emsewreinch/gesturaware-kasa/Ekran görüntüsü 2026-09-13 182619.png

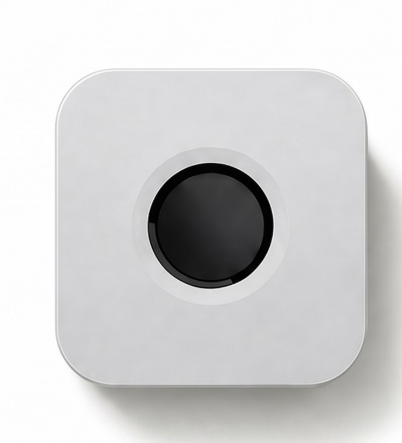
Ekran görüntüsü 2026-09-13 182619.png
