emsewreinch/gesturaware-kasa/kontrolcukasa.scad

// =============================================================
// GesturAware - KONTROLCU KASASI (Controller Edition)
//
// Oyun kontrolcusunun arkasina takilan premium kasa.
// Dis olculer Cihazkasaguncel.scad ile AYNI: 64.74 x 53.5 x 20.6 mm.
// PCB: pcb_v1_headers_z.stl (45 x 40 x 1.6 mm, M2 delikler 39 x 34).
//
// 2 parca, ikisi de destek (support) olmadan basilir:
//
//   KAPAK : ust parca. 45 derece pahli ust kenar, buton cevresinde
//           hale halkasi ve iki yanda "(( o ))" jest dalgalari (oyma).
//           Ic dudak govdeye girer, snap toplariyla kilitlenir ve
//           tirnaklariyla PCB'yi yukaridan bastirir.
//   GOVDE : alt parca. USB-C, LED, sensor/reset delikleri, PCB rafi,
//           PCB v1 montaj deliklerinin altinda ayaklar ve tabandan
//           havsali M2 vida delikleri.
//
// Tum olculer mm. Z=0 kasanin (govdenin) en alti.
// USB-C on (-Y), LED arka (+Y) duvarda.
// =============================================================

$fa = 4;
$fs = 0.35;


// =============================================================
// BILESEN / PCB OLCULERI  (PCB v1, pcb_v1_headers_z.stl'den)
// PCB kasada USB kenari one (-Y) bakacak sekilde, 90 derece
// dondurulmus durur: 40 mm kenar kasada X, 45 mm kenar Y.
// =============================================================

pcb_edge_usb = 40;         // PCB X boyu (USB kenari)
pcb_depth    = 45;         // PCB Y boyu
pcb_thick    = 1.6;
pcb_comp_h   = 6.6;        // PCB ustu en yuksek komponent (buton)

hole_ax = 17;              // PCB montaj delikleri X yari-araligi (34 mm)
hole_ay = 19.5;            // PCB montaj delikleri Y yari-araligi (39 mm)
pcb_hole_d = 2.2;          // PCB delik capi (M2)

usb_edge_off = 8.76;       // USB-C merkezinin PCB merkezinden X kacikligi
usb_cx       = -0.4;       // USB-C acikligi X (PCB bunu takip eder)
usb_z_kart   = 3.25;       // USB-C merkezinin PCB alt yuzunden yuksekligi
pcb_cy       = -0.7;       // PCB merkezi Y (USB-C on duvara ~0.5 mm yakin)

usb_w     = 9.2;           // USB-C acikligi X
usb_bos_h = 3.4;           // USB-C acikligi Z
usb_r     = 1.7;

usb_agiz_w     = 10.5;     // on agiz (kablo govdesi) flare
usb_agiz_h     = 7.0;
usb_agiz_r     = 2.5;
usb_agiz_derin = 2;

floor_gap = 2.0;           // PCB alti bosluk (ayak yuksekligi)

et = 2;                    // duvar kalinligi
tavan_et = 2.6;            // kapak tavani (oyuk altinda 1.4 mm kalir)

buton_cap = 12;            // ust buton deligi
buton_x   = 0;
buton_y   = 0;

sensor_cap = 5.0;          // alt sensor deligi
reset_cap  = 1.0;          // alt reset deligi

led_cap = 5.0;             // arka 5 mm LED
led_x   = 18;
led_z   = 10;


// =============================================================
// DIS OLCULER (Cihazkasaguncel.scad ile ayni, sabit)
// =============================================================

uzunluk     = 64.74;                      // X
genislik    = 53.5;                       // Y
toplam_yuks = 20.6;                       // Z


// =============================================================
// TURETILEN OLCULER
// =============================================================

bd_cx   = usb_cx - usb_edge_off;          // PCB merkezi X (-9.16)
bd_cy   = pcb_cy;                         // PCB merkezi Y
board_l = bd_cx - pcb_edge_usb / 2;
board_r = bd_cx + pcb_edge_usb / 2;
board_f = bd_cy - pcb_depth / 2;          // on kenar (USB tarafi)
board_b = bd_cy + pcb_depth / 2;          // arka kenar

z_rest    = et + floor_gap;               // PCB alt yuzu  (4.0)
z_pcb_top = z_rest + pcb_thick;           // PCB ust yuzu  (5.6)
tavan_z   = toplam_yuks - tavan_et;       // tavan ic yuzu (18.0)

usb_alt = z_rest + usb_z_kart - usb_bos_h / 2;   // 5.55
usb_z0 = usb_alt;
usb_z1 = usb_alt + usb_bos_h;

hx = uzunluk / 2;                         // dis yari X
hy = genislik / 2;                        // dis yari Y
ix = hx - et;                             // ic yari X
iy = hy - et;                             // ic yari Y


// =============================================================
// TASARIM
// =============================================================

kose_r  = 6;      // plan kose radiusu. 8 -> 6: ic kose r=4 olur, PCB'nin
                  // keskin koseleri bile duvara degmez (0.46 mm pay).
ic_r    = kose_r - et;

ust_pah = 2.0;    // ust kenar 45 derece pah (bed'e bakan yuz, destek gerekmez)
ek_z    = 13;     // kapak/govde birlesimi. USB-C ve LED tamamen govdede kalir.
ek_pah  = 0.6;    // birlesim cizgisindeki V-oluk (golge cizgisi)
giris_pah = 0.5;  // govde ust ic kenari: kapak dudagi icin giris pahi
alt_pah = 0.8;    // on / arka alt kenar pahi

// kapak ic pahi: pah boyunca da duvar kalinligi = et kalsin
ic_pah = max(ust_pah - et * (2 - sqrt(2)), 0.2);


// -------------------------------------------------------------
// Ust yuzey oymalari (kapak ters basildigi icin ilk katmanlarda)
// Oyuklara ayri basilan renkli dolgu (inlay) parcalari oturur:
// inlay, oyugun her kenarindan inlay_bosluk kadar kucuk basilir.
// -------------------------------------------------------------

oyma_on    = true;
oyma_derin  = 1.2;                // 6 katman (0.2 mm katmanla); inlay yuksekligi de bu
inlay_bosluk = 0.14;              // inlay her kenardan bu kadar kucuk (0.12 - 0.16)

hale_r = 9;                       // buton cevresi halka (orta cizgi)
hale_w = 1.6;                     // 0.4 nozulla dolgu 3 cizgi

dalga_r   = [13, 16.5, 20];       // "(( o ))" jest dalgalari
dalga_w   = 1.6;
dalga_aci = 34;                   // her yayin yari acisi (derece)

buton_pah = 0.4;                  // buton deligi ust kenar pahi


// -------------------------------------------------------------
// Kapak ic dudagi + PCB bastirma tirnaklari
// Dudak govde duvari icinde, PCB ustunden 0.1 mm yukarida biter.
// -------------------------------------------------------------

dudak_et     = 1.0;
dudak_bosluk = 0.2;
pcb_ust_pay  = 0.1;               // dudak alti / tirnak ile PCB ustu arasi

tirnak_on       = true;           // PCB bastirma tirnaklari
tirnak_w        = 4;
tirnak_bindirme = 0.7;            // PCB kenarinin ustune binme
// montaj deliklerinin yanina (bakir/komponent bosluk bolgesi)
tirnak_x = [bd_cx - hole_ax + 1, bd_cx + hole_ax + 1];

dudak_dis_x = ix - dudak_bosluk;
dudak_dis_y = iy - dudak_bosluk;
dudak_ic_x  = dudak_dis_x - dudak_et;
dudak_ic_y  = dudak_dis_y - dudak_et;
dudak_alt   = z_pcb_top + pcb_ust_pay;
dudak_r     = ic_r - dudak_bosluk;

// on dudakta centik X araligi: PCB v1 on kenarindan tasan konnektorler
// (kasada X -18.7 .. 4.1, Z 8.9'a kadar)
dudak_on_centik = [bd_cx - 10.5, usb_cx + 5.5];


// -------------------------------------------------------------
// PCB rafi: PCB kenarlarini alttan tasir (sol, on, arka, sag kenar).
// Ic cubuk / kolon yok.
// -------------------------------------------------------------

raf_bindirme = 1.0;               // rafin PCB kenarinin altina girmesi
raf_usb_w    = 12;                // USB konnektoru altinda raf yok


// -------------------------------------------------------------
// Snap - vidasiz kenetlenme (eski dosyadaki ile ayni mantik)
// Kapak dudagindaki toplar, govde ic duvarindaki yuvalara oturur.
// -------------------------------------------------------------

snap_on       = true;
snap_x        = [-23, 24];        // on ve arka duvarda X konumlari (on centigin disinda)
snap_z        = 10;
snap_d        = 2.4;
snap_pocket_d = 2.9;
snap_int      = 0.4;              // sikilik - artir = daha sert klik


// -------------------------------------------------------------
// PCB montaji: PCB v1 deliklerinin altinda ayaklar, tabandan havsali
// M2 vida (M2x8 havsa bas + somun PCB ustunde).
// -------------------------------------------------------------

vida_on     = true;
vida_d      = 2.4;                // M2 gecis deligi
havsa_d     = 4.4;                // M2 havsa bas capi
havsa_derin = 1.1;
ayak_d      = 5.0;                // PCB alti ayak capi


// -------------------------------------------------------------
// Alt yazi (govde tabaninda, disaridan okunur)
// -------------------------------------------------------------

yazi_on   = true;
yazi      = "GESTURAWARE";
yazi_boy  = 3.2;
yazi_derin = 0.4;
yazi_y    = -9;
yazi_font = "Liberation Sans:style=Bold";


// =============================================================
// YARDIMCI MODULLER / FONKSIYONLAR
// =============================================================

module rrect(l, w, r)
{
    rr = max(min(r, l / 2, w / 2), 0.1);

    hull()
        for (sx = [-1, 1], sy = [-1, 1])
            translate([sx * (l / 2 - rr), sy * (w / 2 - rr)])
                circle(r = rr);
}


module rdilim(l, w, r, z)
{
    translate([0, 0, z])
        linear_extrude(height = 0.01)
            rrect(l, w, r);
}


// yay bandi, +X ekseni etrafinda -a..+a derece, uclari yuvarlak
module yay2d(r, w, a)
{
    R = 2 * (r + w);

    intersection()
    {
        difference()
        {
            circle(r = r + w / 2, $fn = 200);
            circle(r = r - w / 2, $fn = 200);
        }

        polygon(concat([[0, 0]], [for (t = [-a : 2 : a]) [R * cos(t), R * sin(t)]]));
    }

    for (s = [-1, 1])
        rotate(s * a)
            translate([r, 0])
                circle(d = w, $fn = 24);
}


// =============================================================
// KAPAK (UST PARCA)
// =============================================================

module kapak()
{
    union()
    {
        difference()
        {
            kapak_dis();
            kapak_ic();
            buton_bosluk();

            if (oyma_on)
                ust_oyma();
        }

        dudak();
    }
}


module kapak_dis()
{
    hull()
    {
        // alt kenar: birlesim V-olugunun ust yarisi
        rdilim(uzunluk - 2 * ek_pah, genislik - 2 * ek_pah, kose_r - ek_pah, ek_z);

        translate([0, 0, ek_z + ek_pah])
            linear_extrude(height = toplam_yuks - ust_pah - ek_z - ek_pah)
                rrect(uzunluk, genislik, kose_r);

        // ust yuzey (45 derece pah)
        rdilim(uzunluk - 2 * ust_pah, genislik - 2 * ust_pah, kose_r - ust_pah,
               toplam_yuks - 0.01);
    }
}


module kapak_ic()
{
    hull()
    {
        translate([0, 0, ek_z - 1])
            linear_extrude(height = tavan_z - ic_pah - (ek_z - 1))
                rrect(2 * ix, 2 * iy, ic_r);

        rdilim(2 * (ix - ic_pah), 2 * (iy - ic_pah), ic_r - ic_pah, tavan_z - 0.01);
    }
}


module buton_bosluk()
{
    translate([buton_x, buton_y, tavan_z - 0.1])
        cylinder(h = tavan_et + 0.2, d = buton_cap);

    // ust kenar pahi
    translate([buton_x, buton_y, toplam_yuks - buton_pah])
        cylinder(h = buton_pah + 0.01, d1 = buton_cap, d2 = buton_cap + 2 * buton_pah + 0.02);
}


module ust_oyma_2d()
{
    // hale halkasi
    difference()
    {
        circle(r = hale_r + hale_w / 2, $fn = 160);
        circle(r = hale_r - hale_w / 2, $fn = 160);
    }

    // "(( o ))" jest dalgalari - sol ve sag
    for (a = [0, 180])
        rotate(a)
            for (r = dalga_r)
                yay2d(r, dalga_w, dalga_aci);
}


// oyma hacmi (kapaktan cikarilir)
module ust_oyma()
{
    translate([buton_x, buton_y, toplam_yuks - oyma_derin])
        linear_extrude(height = oyma_derin + 0.01)
            ust_oyma_2d();
}


// -------------------------------------------------------------
// Ic dudak: govdenin icine girer. Ust ucu 45 derece omuzla kapak
// duvarina baglanir (ters baskida sarkma olmaz).
// -------------------------------------------------------------

module dudak()
{
    omuz = dudak_et + dudak_bosluk;

    difference()
    {
        union()
        {
            translate([0, 0, dudak_alt])
                linear_extrude(height = ek_z - dudak_alt + 0.01)
                    rrect(2 * dudak_dis_x, 2 * dudak_dis_y, dudak_r);

            translate([0, 0, ek_z])
                linear_extrude(height = omuz + 0.3)
                    rrect(2 * ix + 0.02, 2 * iy + 0.02, ic_r + 0.01);
        }

        translate([0, 0, dudak_alt - 1])
            linear_extrude(height = ek_z - dudak_alt + 1.01)
                rrect(2 * dudak_ic_x, 2 * dudak_ic_y, dudak_r - dudak_et);

        // 45 derece omuz: dudak ic yuzunden kapak ic duvarina
        hull()
        {
            rdilim(2 * dudak_ic_x, 2 * dudak_ic_y, dudak_r - dudak_et, ek_z);

            translate([0, 0, ek_z + omuz])
                linear_extrude(height = 1)
                    rrect(2 * ix, 2 * iy, ic_r);
        }

        // PCB on kenarindan tasan USB-C ve konnektor icin centik
        translate([dudak_on_centik[0], -hy, dudak_alt - 1])
            cube([dudak_on_centik[1] - dudak_on_centik[0], 5, usb_z1 + 1 - (dudak_alt - 1)]);

        // LED govdesi / flansi icin centik
        translate([led_x - 3.5, hy - 5, dudak_alt - 1])
            cube([7, 5, ek_z - (dudak_alt - 1)]);
    }

    snap_toplari();

    if (tirnak_on)
        pcb_tirnaklari();
}


module snap_toplari()
{
    if (snap_on)
        for (sx = snap_x, sy = [-1, 1])
            intersection()
            {
                translate([sx, sy * (iy + snap_int - snap_d / 2), snap_z])
                    sphere(d = snap_d, $fn = 32);

                // sadece disa dogru cikan kisim (PCB tarafina tasmaz)
                translate([sx - snap_d, sy > 0 ? dudak_ic_y : -hy - 1, snap_z - snap_d])
                    cube([2 * snap_d, hy + 1 - dudak_ic_y, 2 * snap_d]);
            }
}


// PCB'yi raf uzerine bastiran kucuk tirnaklar (ustu 45 derece)
module pcb_tirnaklari()
{
    h0 = 0.2;

    // sy: -1 on kenar, +1 arka kenar
    for (tx = tirnak_x, sy = [-1, 1])
    {
        y_kok = dudak_ic_y + 0.01;
        y_uc  = sy * (sy < 0 ? board_f : board_b) - tirnak_bindirme;

        mirror([0, sy < 0 ? 1 : 0, 0])
            translate([tx, 0, 0])
                rotate([90, 0, 90])
                    linear_extrude(height = tirnak_w, center = true)
                        polygon([
                            [y_kok, dudak_alt],
                            [y_uc,  dudak_alt],
                            [y_uc,  dudak_alt + h0],
                            [y_kok, dudak_alt + h0 + (y_kok - y_uc)]
                        ]);
    }
}


// =============================================================
// GOVDE (ALT PARCA)
// =============================================================

module govde()
{
    difference()
    {
        union()
        {
            difference()
            {
                govde_dis();
                govde_ic();
            }

            intersection()
            {
                pcb_raf();
                govde_dis();
            }

            if (vida_on)
                pcb_ayaklari();
        }

        usb_bosluk();
        led_delik();
        snap_cepleri();

        if (vida_on)
            vida_delikleri();

        // sensor deligi
        translate([0, 0, -1])
            cylinder(h = et + 2, d = sensor_cap);

        // reset deligi
        translate([bd_cx, -hole_ay - 2, -1])
            cylinder(h = et + 2, d = reset_cap, $fn = 24);

        if (yazi_on)
            alt_yazi();
    }
}


module govde_dis()
{
    hull()
    {
        // alt kenar pahi
        rdilim(uzunluk - 2 * alt_pah, genislik - 2 * alt_pah, kose_r - alt_pah, 0);

        translate([0, 0, alt_pah])
            linear_extrude(height = ek_z - ek_pah - alt_pah)
                rrect(uzunluk, genislik, kose_r);

        // ust: birlesim V-olugunun alt yarisi
        rdilim(uzunluk - 2 * ek_pah, genislik - 2 * ek_pah, kose_r - ek_pah, ek_z - 0.01);
    }
}


module govde_ic()
{
    translate([0, 0, et])
        linear_extrude(height = ek_z + 5)
            rrect(2 * ix, 2 * iy, ic_r);

    // ust ic kenarda giris pahi: kapak dudagi kolay oturur
    hull()
    {
        rdilim(2 * ix, 2 * iy, ic_r, ek_z - giris_pah);
        rdilim(2 * (ix + giris_pah), 2 * (iy + giris_pah), ic_r + giris_pah, ek_z + 0.01);
    }
}


module pcb_raf()
{
    translate([0, 0, et - 0.01])
        linear_extrude(height = z_rest - et + 0.01)
            difference()
            {
                intersection()
                {
                    rrect(2 * ix, 2 * iy, ic_r);

                    translate([-hx - 1, -hy - 1])
                        square([board_r + raf_bindirme + hx + 1, genislik + 2]);
                }

                translate([board_l + raf_bindirme, board_f + raf_bindirme])
                    square([pcb_edge_usb - 2 * raf_bindirme, pcb_depth - 2 * raf_bindirme]);

                // USB konnektoru altinda raf yok
                translate([usb_cx - raf_usb_w / 2, -hy - 1])
                    square([raf_usb_w, board_f + 3 + hy + 1]);
            }
}


// On yuzde ince USB kesit dilimi (flare hull'u icin)
module usb_dilim(y, w, h, r)
{
    translate([usb_cx, y, (usb_z0 + usb_z1) / 2])
        rotate([-90, 0, 0])
            linear_extrude(height = 0.01)
                rrect(w, h, r);
}


module usb_bosluk()
{
    // standart USB-C gecis yuvasi
    translate([usb_cx, -genislik / 2 - 2, (usb_z0 + usb_z1) / 2])
        rotate([-90, 0, 0])
            linear_extrude(height = et + 4)
                rrect(usb_w, usb_bos_h, usb_r);

    // on agiz flare (kablo govdesi icin)
    hull()
    {
        usb_dilim(-genislik / 2 - 0.02, usb_agiz_w, usb_agiz_h, usb_agiz_r);
        usb_dilim(-genislik / 2 + usb_agiz_derin, usb_w, usb_bos_h, usb_r);
    }
}


module led_delik()
{
    translate([led_x, hy + 1, led_z])
        rotate([90, 0, 0])
            cylinder(h = et + 2, d = led_cap, $fn = 48);

    // dis kenar pahi
    translate([led_x, hy + 0.01, led_z])
        rotate([90, 0, 0])
            cylinder(h = 0.5, d1 = led_cap + 1, d2 = led_cap, $fn = 48);
}


module snap_cepleri()
{
    if (snap_on)
        for (sx = snap_x, sy = [-1, 1])
            translate([sx, sy * (iy + snap_int - snap_d / 2), snap_z])
                sphere(d = snap_pocket_d, $fn = 32);
}


function pcb_delikleri() =
    [for (sx = [-1, 1], sy = [-1, 1]) [bd_cx + sx * hole_ax, bd_cy + sy * hole_ay]];


// PCB'nin oturdugu ayaklar (tabandan PCB altina, 2 mm)
module pcb_ayaklari()
{
    for (p = pcb_delikleri())
        translate([p[0], p[1], et - 0.01])
            cylinder(h = z_rest - et + 0.01, d = ayak_d, $fn = 40);
}


// tabandan havsali M2 gecis delikleri
module vida_delikleri()
{
    for (p = pcb_delikleri())
        translate([p[0], p[1], 0])
        {
            translate([0, 0, -1])
                cylinder(h = z_rest + 2, d = vida_d, $fn = 32);

            translate([0, 0, -0.01])
                cylinder(h = havsa_derin + 0.01, d1 = havsa_d, d2 = vida_d, $fn = 40);
        }
}


// ayri basilan renkli dolgu: oyuktan inlay_bosluk kadar kucuk, oyma_derin yuksek
module inlay()
{
    translate([buton_x, buton_y, toplam_yuks - oyma_derin])
        linear_extrude(height = oyma_derin)
            offset(delta = -inlay_bosluk)
                ust_oyma_2d();
}


module alt_yazi()
{
    translate([0, yazi_y, -0.01])
        linear_extrude(height = yazi_derin + 0.01)
            mirror([1, 0, 0])
                text(yazi, size = yazi_boy, font = yazi_font,
                     halign = "center", valign = "center", spacing = 1.08);
}


// =============================================================
// PCB HAYALETI (sadece gorsel kontrol icin)
// =============================================================

module pcb_hayalet()
{
    color([0.05, 0.35, 0.2, 0.9])
        translate([board_l, board_f, z_rest])
            cube([pcb_edge_usb, pcb_depth, pcb_thick]);

    color([0.9, 0.9, 0.9, 0.35])
        translate([board_l + 1, board_f + 1, z_pcb_top])
            cube([pcb_edge_usb - 2, pcb_depth - 2, pcb_comp_h]);

    color("Silver")
        translate([usb_cx - 4.47, board_f - 1.07, (usb_z0 + usb_z1) / 2 - 1.6])
            cube([8.94, 7.35, 3.2]);
}


// =============================================================
// GORUNUM SECICI
//
// "montaj"      = kapak + govde (varsayilan)
// "patlatilmis" = parcalar ayrik, ust uste
// "kesit"       = montajin X=... kesiti (ic yapi kontrolu)
// "kapak" / "govde" = tek parca, montaj konumunda
// "baski"       = iki parca baski yonunde yan yana
// "kapak_baski" / "govde_baski" = tek parca, STL icin
// "inlay_baski" = oyuklara bastirilan renkli dolgu parcalari (ayri baski)
// "yok"         = hicbir sey (include ile kullanim icin)
// =============================================================

goster = "montaj";

pcb_goster = false;          // montaj gorunumlerinde PCB hayaleti

renk_kapak = [0.16, 0.17, 0.19];
renk_govde = [0.24, 0.25, 0.28];
renk_vurgu = [0.00, 0.85, 1.00];


module renkli_kapak()
{
    color(renk_kapak) kapak();

    if (oyma_on)
        color(renk_vurgu)
            translate([0, 0, -0.02])
                inlay();
}


module kapak_baski_yonu()
{
    translate([0, 0, toplam_yuks])
        rotate([180, 0, 0])
            children();
}


if (goster == "kapak")
{
    renkli_kapak();
}
else if (goster == "govde")
{
    color(renk_govde) govde();
}
else if (goster == "patlatilmis")
{
    translate([0, 0, 22]) renkli_kapak();
    color(renk_govde) govde();

    if (pcb_goster) translate([0, 0, 9]) pcb_hayalet();
}
else if (goster == "kesit")
{
    difference()
    {
        union()
        {
            renkli_kapak();
            color(renk_govde) govde();
        }

        translate([-hx - 5, 0, -10])
            cube([uzunluk + 10, hy + 5, toplam_yuks + 20]);
    }

    if (pcb_goster) pcb_hayalet();
}
else if (goster == "kapak_baski")
{
    kapak_baski_yonu() kapak();
}
else if (goster == "inlay_baski")
{
    // tablaya duz, Z = 0 .. oyma_derin
    translate([0, 0, -(toplam_yuks - oyma_derin)])
        inlay();
}
else if (goster == "govde_baski")
{
    govde();
}
else if (goster == "yok")
{
    // hicbir sey cizme (include ile kullanim / testler icin)
}
else if (goster == "baski")
{
    translate([-(uzunluk + 6), 0, 0]) color(renk_kapak) kapak_baski_yonu() kapak();
    color(renk_govde) govde();
}
else
{
    // montaj
    renkli_kapak();
    color(renk_govde) govde();

    if (pcb_goster) pcb_hayalet();
}


// =============================================================
// BILGI
// =============================================================

echo(str("KASA DIS: ", uzunluk, " X ", genislik, " X ", toplam_yuks, " mm"));
echo(str("PCB X = [", board_l, " .. ", board_r, "]  Y = [", board_f, " .. ", board_b,
         "]  USB X = ", usb_cx, "  USB Z = [", usb_z0, " .. ", usb_z1, "]"));
